Yusufii9/Pediatric-Laparoscopic-Surgery-Simulator/Software/simulator/HSV.py

"""
HSV.py allows a user to find an appropriate HSV range for detecting a colour of choice

Code from:
https://toptechboy.com/tracking-an-object-based-on-color-in-opencv/
"""

import cv2
import numpy as np

print(cv2.__version__)


def onTrack1(val):
    global hueLow
    hueLow = val
    print("Hue Low", hueLow)


def onTrack2(val):
    global hueHigh
    hueHigh = val
    print("Hue High", hueHigh)


def onTrack3(val):
    global satLow
    satLow = val
    print("Sat Low", satLow)


def onTrack4(val):
    global satHigh
    satHigh = val
    print("Sat High", satHigh)


def onTrack5(val):
    global valLow
    valLow = val
    print("Val Low", valLow)


def onTrack6(val):
    global valHigh
    valHigh = val
    print("Val High", valHigh)


width = 640
height = 360
cam = cv2.VideoCapture(1, cv2.CAP_DSHOW)
cam.set(cv2.CAP_PROP_FRAME_WIDTH, width)
cam.set(cv2.CAP_PROP_FRAME_HEIGHT, height)
cam.set(cv2.CAP_PROP_FPS, 30)
cam.set(cv2.CAP_PROP_FOURCC, cv2.VideoWriter_fourcc(*"MJPG"))

cv2.namedWindow("myTracker")
cv2.moveWindow("myTracker", width, 0)

hueLow = 10
hueHigh = 20
satLow = 10
satHigh = 250
valLow = 10
valHigh = 250

cv2.createTrackbar("Hue Low", "myTracker", 10, 179, onTrack1)
cv2.createTrackbar("Hue High", "myTracker", 20, 179, onTrack2)
cv2.createTrackbar("Sat Low", "myTracker", 10, 255, onTrack3)
cv2.createTrackbar("Sat High", "myTracker", 250, 255, onTrack4)
cv2.createTrackbar("Val Low", "myTracker", 10, 255, onTrack5)
cv2.createTrackbar("Val High", "myTracker", 250, 255, onTrack6)

while True:
    ignore, frame = cam.read()
    frameHSV = cv2.cvtColor(frame, cv2.COLOR_BGR2HSV)
    lowerBound = np.array([hueLow, satLow, valLow])
    upperBound = np.array([hueHigh, satHigh, valHigh])
    myMask = cv2.inRange(frameHSV, lowerBound, upperBound)
    # myMask=cv2.bitwise_not(myMask)
    myObject = cv2.bitwise_and(frame, frame, mask=myMask)
    myObjectSmall = cv2.resize(myObject, (int(width / 2), int(height / 2)))
    cv2.imshow("My Object", myObjectSmall)
    cv2.moveWindow("My Object", int(width / 2), int(height))
    myMaskSmall = cv2.resize(myMask, (int(width / 2), int(height / 2)))

    contours, _ = cv2.findContours(myMask, cv2.RETR_EXTERNAL, cv2.CHAIN_APPROX_SIMPLE)

    height, width, _ = frame.shape
    min_x, min_y = width, height
    max_x = max_y = 0

    #  max_contour = contours[0]
    for cnt in contours:
        area = cv2.contourArea(cnt)

        if area > 150:
            M = cv2.moments(cnt)
            cX = int(M["m10"] / M["m00"])
            cY = int(M["m01"] / M["m00"])
            #  cv2.drawContours(frame, [cnt], -1, (0, 255, 0), 2)
            # cv2.circle(frame, (cX, cY), 7, (255, 255, 255), -1)
            coords = str(cX) + ", " + str(cY)
            (x, y, w, h) = cv2.boundingRect(cnt)
            min_x, max_x = min(x, min_x), max(x + w, max_x)
            min_y, max_y = min(y, min_y), max(y + h, max_y)
            cv2.rectangle(
                frame, (x - 20, y - 20), (x + 20 + w, y + 20 + h), (255, 0, 0), 2
            )
            # cv2.floodFill(frame, np.zeros((height + 2, width + 2), np.uint8), (0, 0), 0)

            cv2.putText(
                frame, coords, (cX, cY), cv2.FONT_HERSHEY_SIMPLEX, 1, (0, 0, 255), 2
            )

    cv2.imshow("My Mask", myMaskSmall)
    cv2.moveWindow("My Mask", 0, height)
    cv2.imshow("my WEBcam", frame)
    cv2.moveWindow("my WEBcam", 0, 0)
    if cv2.waitKey(1) & 0xFF == ord("q"):
        break
cam.release()
